y1zzz0811/GongChuangSai_Repository_New/参考资料/参考代码/视觉识别/视觉代码gxwl4看1抓1/detect_color.py

import cv2 as cv
import numpy as np
import configparser


class Color_detect():
    def __init__(self):
        config = configparser.ConfigParser()  # 类实例化
        # 定义文件路径
        path = 'config.ini'
        config.read(path)

        red_threshold = list(
            map(int, config.get('using', 'red_hsv')[1:-1].split(',')))  # 红色阈值
        green_threshold = list(
            map(int, config.get('using', 'green_hsv')[1:-1].split(',')))  # 绿色阈值
        blue_threshold = list(
            map(int, config.get('using', 'blue_hsv')[1:-1].split(',')))  # 蓝色阈值
        # print(red_threshold[3])
        self.threshold_r = [red_threshold, green_threshold, blue_threshold]
        # self.color = [(0, 0, 255), (0, 0, 255), (0, 255, 0), (255, 0, 0)]

    def detect(self, hsv_image, threshold_value):
        up_ = np.array(threshold_value[-3:])
        lower_ = np.array(threshold_value[:3])
        mask = cv.inRange(hsv_image, lower_, up_)
        kernel = np.ones((3, 3), np.uint8)
        dilation = cv.dilate(mask, kernel, iterations=1)
        cnts = cv.findContours(
            dilation, cv.RETR_EXTERNAL, cv.CHAIN_APPROX_NONE)
        area = 1500
        blob = None
        #max_area = 99999
        for c in cnts[0]:
            area_img = abs(cv.contourArea(c, True))
            #cv.drawContours(hsv_image, [c], 0, (255, 0, 0), 2)
            # print(area_img)
            if area_img > area:
                # print(area_img)
                blob = c
                area = area_img
        # cv.imshow("dilation", dilation)
        # cv.imshow("hsv_image", hsv_image)
        if blob is not None:
            # Draw a rect around the blob.
            rect = cv.minAreaRect(blob)
            # cv.boxPoints(rect) for OpenCV 3.x 获取最小外接矩形的4个顶点
            box = cv.boxPoints(rect)
            box = np.int0(box)
            #print("四个顶点坐标为;", box)
            return True, area
        return False, None

    def run(self, img):
        # roi =  img[y:y+h, x:x+w]
        box = [0, 0, 0]
        hsv = cv.cvtColor(img, cv.COLOR_BGR2HSV)
        found_color = False  # 添加一个标志来指示是否找到了颜色
        for i in range(len(self.threshold_r)):
            _ret, _box = self.detect(hsv, self.threshold_r[i])
            if _ret:
                # cv.drawContours(img, _box, -1, self.color[i], 3)
                box[i] = _box
                found_color = True  # 找到颜色，将标志设置为True
        if not found_color:
            return None
        else:
            num = box.index(max(box))
            return str(4-(num + 1))



if __name__ == '__main__':
    C_d = Color_detect()

    maix = True
    camera = cv.VideoCapture(0)
    camera.set(cv.CAP_PROP_FRAME_WIDTH, 160)
    camera.set(cv.CAP_PROP_FRAME_HEIGHT, 120)
    camera.set(cv.CAP_PROP_BUFFERSIZE, 1)
    camera.set(cv.CAP_PROP_AUTO_WB, 0)
    if maix:
        f = open('/dev/fb0', 'wb')
    while True:
        # 读取当前帧
        ret, frame = camera.read()

        # print(ret.shape)
        if not ret:
            print("frame is empty.")
            continue
        # frame1 = cv.imread("./qr_test.png")
        hsv = cv.cvtColor(frame, cv.COLOR_BGR2HSV)
        for i in range(len(C_d.threshold_r)):
            _ret, _box = C_d.detect(hsv, C_d.threshold_r[i])
            # if _ret:
            #     cv.drawContours(frame, _box, -1, C_d.color[i], 3)

        if maix:
            frame = cv.resize(frame, (240, 240))
            dst = cv.cvtColor(frame, cv.COLOR_BGR2BGR565)
            # cv.imshow('frame', frame)

            f.seek(0)
            f.write(bytearray(dst))
        else:
            cv.imshow("camera", frame)

        if(cv.waitKey(5) == 27):
            break
    camera.release()
    cv.destroyAllWindows()
