y1zzz0811/GongChuangSai_Repository_New/参考资料/参考代码/底盘控制程序包/User/Task/inc/Servo.h

extern void IdentifyColor_action(void);
extern void IdentifyCircle_action(void);
extern void Rest_action(void);
extern void Rest_action_S2(void);
extern void QR_action(void);

extern void Get_A(void);
extern void Get_B(void);

extern void Put_1(void);
extern void Put_2(void);
extern void Put_3(void);

extern void Get_1(void);
extern void Get_2(void);
extern void Get_3(void);

extern void Put_Blue(void);
extern void Put_Green(void);
extern void Put_Red(void);
extern void Put_Blue_Stacking(void);
extern void Put_Green_Stacking(void);
extern void Put_Red_Stacking(void);

extern void Get_Blue(void);
extern void Get_Green(void);
extern void Get_Red(void);
extern void QR_action(void);
