y1zzz0811/GongChuangSai_Repository_New/参考资料/参考代码/底盘控制程序包/User/BSP/src/bsp_lcd_font.c

#include "bsp_lcd_font.h"
/* DejaVu Sans Mono */
/*
  (0) !(1) "(2) #(3) $(4) %(5) &(6) '(7)
 ((8) )(9) *(10) +(11) ,(12) -(13) .(14) /(15)
 0(16) 1(17) 2(18) 3(19) 4(20) 5(21) 6(22) 7(23)
 8(24) 9(25) :(26) ;(27) <(28) =(29) >(30) ?(31)
 @(32) A(33) B(34) C(35) D(36) E(37) F(38) G(39)
 H(40) I(41) J(42) K(43) L(44) M(45) N(46) O(47)
 P(48) Q(49) R(50) S(51) T(52) U(53) V(54) W(55)
 X(56) Y(57) Z(58) [(59) \(60) ](61) ^(62) _(63)
 `(64) a(65) b(66) c(67) d(68) e(69) f(70) g(71)
 h(72) i(73) j(74) k(75) l(76) m(77) n(78) o(79)
 p(80) q(81) r(82) s(83) t(84) u(85) v(86) w(87)
 x(88) y(89) z(90) {(91) |(92) }(93)
*/

#ifdef ASC2_1206
const unsigned char asc2_1206[]={
0x00,0x00,0x00,0x00,0x00,0x00,0x00,0x00,0x00,0x00,0x00,0x00,
0x00,0x00,0x20,0x20,0x20,0x20,0x20,0x20,0x00,0x20,0x00,0x00,
0x00,0x28,0x50,0x50,0x00,0x00,0x00,0x00,0x00,0x00,0x00,0x00,
0x00,0x00,0x28,0x28,0xFC,0x28,0x50,0xFC,0x50,0x50,0x00,0x00,
0x00,0x20,0x78,0xA8,0xA0,0x60,0x30,0x28,0xA8,0xF0,0x20,0x00,
0x00,0x00,0x48,0xA8,0xB0,0x50,0x28,0x34,0x54,0x48,0x00,0x00,
0x00,0x00,0x20,0x50,0x50,0x78,0xA8,0xA8,0x90,0x6C,0x00,0x00,
0x00,0x40,0x40,0x80,0x00,0x00,0x00,0x00,0x00,0x00,0x00,0x00,
0x00,0x04,0x08,0x10,0x10,0x10,0x10,0x10,0x10,0x08,0x04,0x00,
0x00,0x40,0x20,0x10,0x10,0x10,0x10,0x10,0x10,0x20,0x40,0x00,
0x00,0x00,0x00,0x20,0xA8,0x70,0x70,0xA8,0x20,0x00,0x00,0x00,
0x00,0x00,0x20,0x20,0x20,0xF8,0x20,0x20,0x20,0x00,0x00,0x00,
0x00,0x00,0x00,0x00,0x00,0x00,0x00,0x00,0x00,0x40,0x40,0x80,
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
0x00,0x3F,0xFE,0x00,0x00,0x0F,0xF8,0x00,0x00,0x00,0x00,0x00,0x00,0x00,0x00,0x00,
0x00,0x00,0x00,0x00,0x00,0x00,0x00,0x00,0x00,0x00,0x00,0x00,0x00,0x00,0x00,0x00,
0x00,0x00,0x00,0x00,0x00,0x00,0x00,0x00,0x00,0x00,0x00,0x00,0x00,0x00,0x00,0x00,
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
