y1zzz0811/GongChuangSai_Repository_New/参考资料/参考代码/底盘控制程序包/User/VI5300/VI5300_Firmware.c

/* Created by Protons Binary To 'C' Converter V1.00 */
#include "VI5300_Firmware.h"
#include "string.h"
//0x0f02//3842
//v19 //3889
//G01_R03_V01_E//3922
//???
const uint8_t Firmware_Ranging[] = 
{
0x02, 0x0f, 0x46, 0x02, 0x0e, 0xb8, 0xc2, 0x8c, 0xd2, 0xd5, 0x32, 0x02, 0x00, 0x06, 0x53, 0x91, 
0xef, 0x32, 0x00, 0x02, 0x0e, 0x11, 0x8e, 0x29, 0x8f, 0x2a, 0xc2, 0xd5, 0x63, 0x2a, 0xff, 0x63, 
0x29, 0xff, 0x85, 0x29, 0x8c, 0x85, 0x2a, 0x8a, 0xd2, 0x8c, 0x20, 0xd5, 0x12, 0x00, 0x00, 0x00, 
0x00, 0x00, 0x00, 0x00, 0x00, 0x00, 0x00, 0x00, 0x00, 0x00, 0x00, 0x00, 0x00, 0x80, 0xeb, 0x22, 
0x00, 0x00, 0x00, 0x02, 0x00, 0x0e, 0x00, 0x00, 0x00, 0x00, 0x00, 0x02, 0x0a, 0xf0, 0x00, 0x00, 
0x00, 0x00, 0x00, 0x02, 0x08, 0x19, 0x00, 0x00, 0x00, 0x00, 0x00, 0x02, 0x00, 0x5e, 0xc0, 0xe0, 
0xc0, 0xf0, 0xc0, 0x83, 0xc0, 0x82, 0xc0, 0x85, 0xc0, 0x84, 0xc0, 0x86, 0x75, 0x86, 0x00, 0xc0, 
0xd0, 0x75, 0xd0, 0x00, 0xc0, 0x00, 0xc0, 0x01, 0xc0, 0x02, 0xc0, 0x03, 0xc0, 0x04, 0xc0, 0x05, 
0xc0, 0x06, 0xc0, 0x07, 0x53, 0x91, 0x7f, 0x75, 0x97, 0x00, 0x85, 0xbc, 0x08, 0x85, 0xbd, 0x09, 
0xe5, 0x09, 0xae, 0x08, 0x78, 0x02, 0xc3, 0x33, 0xce, 0x33, 0xce, 0xd8, 0xf9, 0x24, 0x00, 0xff, 
0xee, 0x34, 0x08, 0xf5, 0x0c, 0x8f, 0x0d, 0x78, 0x39, 0xe6, 0x60, 0x42, 0xaa, 0x0c, 0xa9, 0x07, 
0x7b, 0x01, 0x90, 0x00, 0x03, 0x12, 0x0c, 0xb4, 0x7f, 0x14, 0x12, 0x0f, 0x07, 0x85, 0x0d, 0x82, 
0x85, 0x0c, 0x83, 0xe0, 0xfd, 0x0f, 0x12, 0x0f, 0x28, 0x78, 0x3d, 0xe6, 0xb4, 0x0f, 0x0c, 0x18, 
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
0xf5, 0x14, 0xee, 0x95, 0x13, 0xf5, 0x13, 0x80, 0x16, 0xe5, 0x09, 0xae, 0x08, 0x78, 0x07, 0xc3, 
0x33, 0xce, 0x33, 0xce, 0xd8, 0xf9, 0x25, 0x14, 0xf5, 0x14, 0xe5, 0x13, 0x3e, 0xf5, 0x13, 0x85, 
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


uint16_t LoadFirmware(void)
{
   return sizeof(Firmware_Ranging);
}
