y1zzz0811/GongChuangSai_Repository_New/参考资料/参考代码/底盘控制程序包/User/BSP/src/bsp_hal_uartdma.c

/* 包含头文件 ----------------------------------------------------------------*/
//Oneself
#include "bsp_hal_uartdma.h"
//C基本库
#include <stdbool.h>	//Bool数据类型
/* 私有宏定义 ----------------------------------------------------------------*/
/**
  * @brief  混合串口实例定义
*/
#ifdef Enabled_MUart1
	UartMixed_TypeDef	muart1;
#endif
#ifdef Enabled_MUart2
	UartMixed_TypeDef	muart2;
#endif
#ifdef Enabled_MUart3
	UartMixed_TypeDef	muart3;
#endif
#ifdef Enabled_MUart4
	UartMixed_TypeDef	muart4;
#endif
#ifdef Enabled_MUart5
	UartMixed_TypeDef	muart5;
#endif
#ifdef Enabled_MUart6
	UartMixed_TypeDef	muart6;
	#define UART6_DIR_TX() HAL_GPIO_WritePin(MAX3485_EN_GPIO_Port, MAX3485_EN_Pin, GPIO_PIN_SET)
  #define UART6_DIR_RX() HAL_GPIO_WritePin(MAX3485_EN_GPIO_Port, MAX3485_EN_Pin, GPIO_PIN_RESET)
#endif
/* 私有类型定义 --------------------------------------------------------------*/

/* 私有变量 ------------------------------------------------------------------*/

/* 扩展变量 ------------------------------------------------------------------*/
 
/* 私有函数原形 --------------------------------------------------------------*/

/* 函数体 --------------------------------------------------------------------*/
/*
if(__HAL_UART_GET_FLAG(&huart2, UART_FLAG_IDLE))
{//检测串口是否产生了空闲中断
    __HAL_UART_CLEAR_IDLEFLAG(&huart2);
    //调用串口接收函数(在uart_mixed中实例化)
    HAL_UART_RxCpltCallback(&huart2);
}
*/
/**
  * @brief  总线方向控制
  * @call   <- HAL_UART_TxCpltCallback(HAL)
  * @call   <- UART_Mixed_TxTrigger(Mixed)
  * @param  muart: 混合串口指针
  * @param  dir: 方向 (true:发送 false:接收)
  * @retval NULL 
**/
void Bsp_UARTDir_Control(UartMixed_TypeDef *muart, bool dir)
{
#if defined(Enabled_MUart1) && defined(UART1_DIR_TX) && defined(UART1_DIR_RX)
	if(muart == &muart1){
		if(dir)		UART1_DIR_TX();
		if(!dir)	UART1_DIR_RX();
	}
#endif
#if defined(Enabled_MUart2) && defined(UART2_DIR_TX) && defined(UART2_DIR_RX)
	if(muart == &muart2){
		if(dir)		UART2_DIR_TX();
		if(!dir)	UART2_DIR_RX();
	}
#endif
#if defined(Enabled_MUart3) && defined(UART3_DIR_TX) && defined(UART3_DIR_RX)
	if(muart == &muart3){
		if(dir)		UART3_DIR_TX();
		if(!dir)	UART3_DIR_RX();
	}
#endif
#if defined(Enabled_MUart4) && defined(UART4_DIR_TX) && defined(UART4_DIR_RX)
	if(muart == &muart4){
		if(dir)		UART4_DIR_TX();
		if(!dir)	UART4_DIR_RX();
	}
#endif
#if defined(Enabled_MUart5) && defined(UART5_DIR_TX) && defined(UART5_DIR_RX)
	if(muart == &muart5){
		if(dir)		UART5_DIR_TX();
		if(!dir)	UART5_DIR_RX();
	}
#endif
#if defined(Enabled_MUart6) && defined(UART6_DIR_TX) && defined(UART6_DIR_RX)
	if(muart == &muart6){
		if(dir)		UART6_DIR_TX();
		if(!dir)	UART6_DIR_RX();
	}
#endif
}
/*********************************************************************/
/****************************    初始化   ****************************/
/*********************************************************************/
/**
  * @brief  混合串口使能初始化
  * @param  muart: 混合串口指针
  * @param  xerc:  接收完成回调函数
  * @param  xetc:  发送完成回调函数
  * @retval NULL 
**/
void Bsp_UartMixed_Init( UartMixed_TypeDef *muart, void(*xerc)(char*, uint16_t), void(*xetc)(void) )
{				     
	memset(muart, 0, sizeof(UartMixed_TypeDef));
	//实例
#ifdef Enabled_MUart1
	if(muart == &muart1){
    	muart1.puart = &huart1;		
	    muart1.pdma_tx = &hdma_usart1_tx;	
	    muart1.pdma_rx = &hdma_usart1_rx;	
	}
#endif
#ifdef Enabled_MUart2
	if(muart == &muart2){
	    muart2.puart = &huart2;		
	    muart2.pdma_tx = &hdma_usart2_tx;	
	    muart2.pdma_rx = &hdma_usart2_rx;	
	}
#endif		
#ifdef Enabled_MUart3
	if(muart == &muart3){
	    muart3.puart = &huart3;		
	    muart3.pdma_tx = &hdma_usart3_tx;	
	    muart3.pdma_rx = &hdma_usart3_rx;	
	}
#endif		
#ifdef Enabled_MUart4
	if(muart == &muart4){
	    muart4.puart = &huart4;		
	    muart4.pdma_tx = &hdma_uart4_tx;
	    muart4.pdma_rx = &hdma_uart4_rx;	
	}
#endif		
#ifdef Enabled_MUart5
	if(muart == &muart5){	
	    muart5.puart = &huart5;		
	    muart5.pdma_tx = &hdma_uart5_tx;	
//	    muart5.pdma_rx = &hdma_uart5_rx;	
	}
#endif	
#ifdef Enabled_MUart6
	if(muart == &muart6){	
	    muart6.puart = &huart6;		
	    muart6.pdma_tx = &hdma_usart6_tx;	
	    muart6.pdma_rx = &hdma_usart6_rx;	
	}
#endif
	//接收回调函数指针
	muart->Xfer_External_RxCallback = xerc;
	muart->Xfer_External_TxCallback = xetc;

	//开始传输
	Bsp_UartMixed_Begin(muart);
}
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
